goldfishlaser/usb-a-magnetic-breakaway/STL Files/STL Archive/dengineering_v02.2.stl

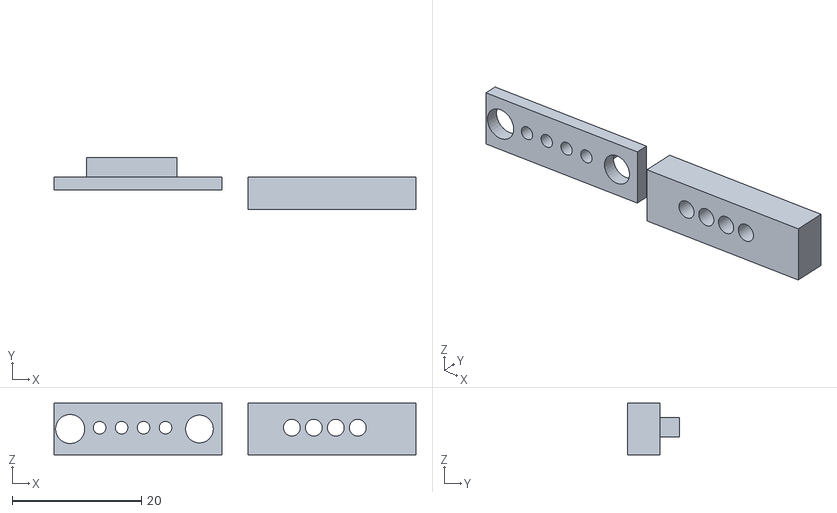
[picture p20: CAD file, 2024-07-27, an earlier design]
STL Files/STL Archive/dengineering_v02.2.stl
56.0 x 8.00 x 8.00
