goldfishlaser/usb-a-magnetic-breakaway/STL Files/STL Archive/mag_startover_v0.2.stl

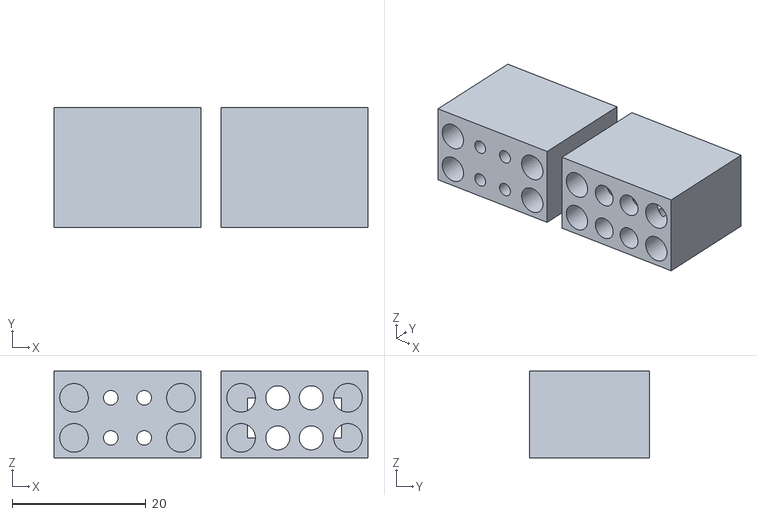
[picture p21: CAD file, 2024-07-27, an earlier design]
STL Files/STL Archive/mag_startover_v0.2.stl
47.0 x 18.0 x 13.0
